ku4qo/MagicBox2.5/images/MagicBoxV2.5-PCBs_StackedFront-1024pix.jpg

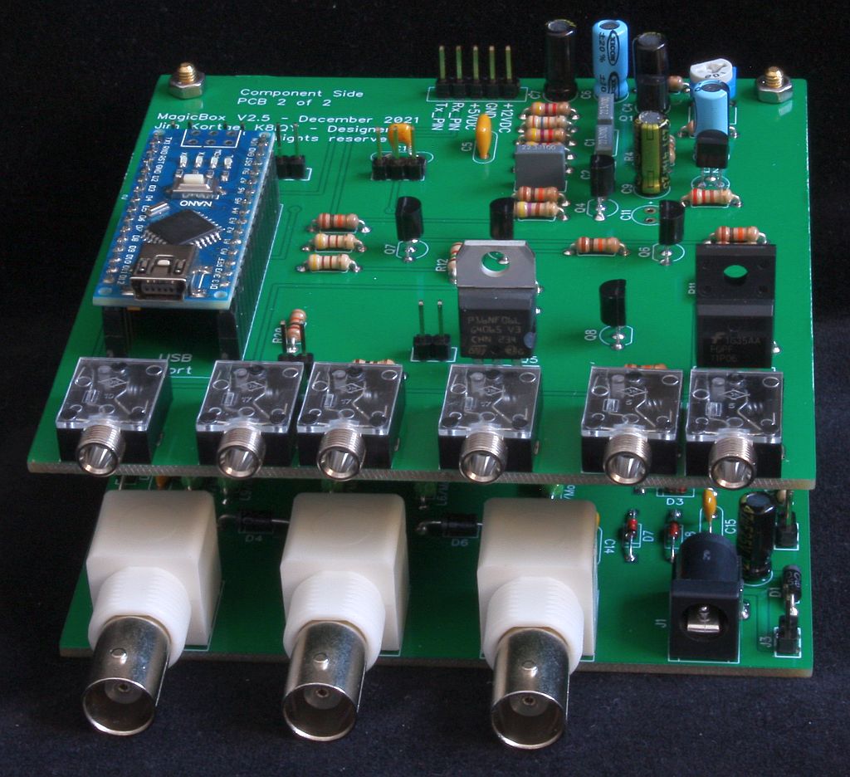
images/MagicBoxV2.5-PCBs_StackedFront-1024pix.jpg
