ku4qo/MagicBox2.5/images/MagicBoxV2.5A-PCB2_Stuffed-1024pix.jpg

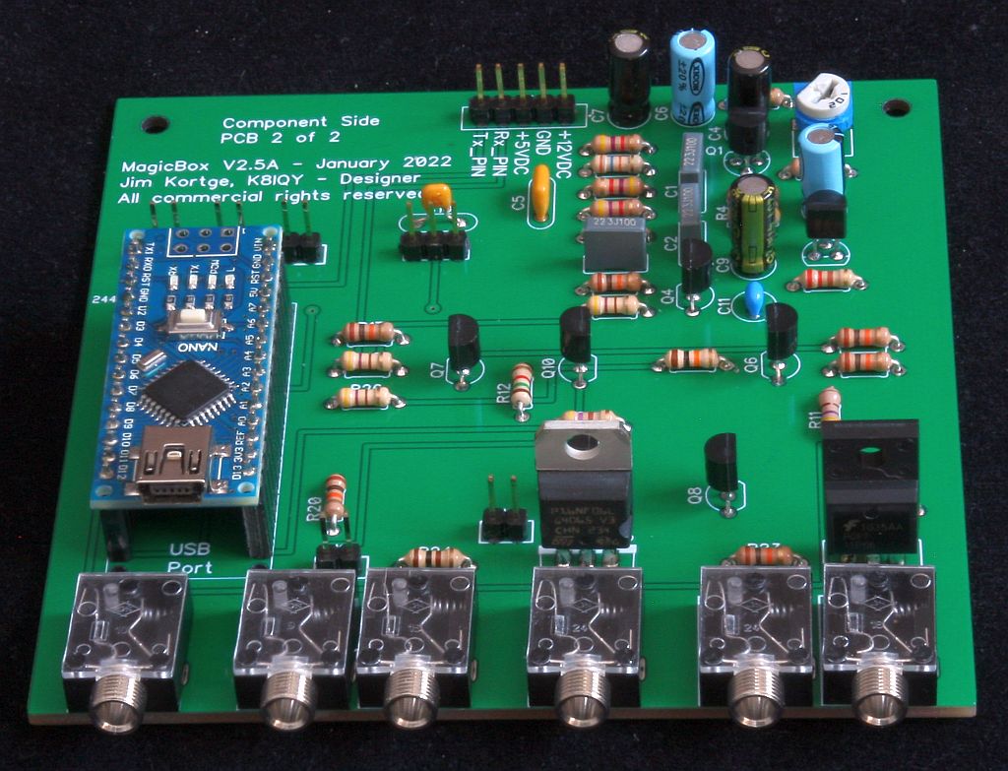
images/MagicBoxV2.5A-PCB2_Stuffed-1024pix.jpg
