ku4qo/MagicBox2.5/images/MagicBoxV2.X-BetaOS-LogicAnalyzer-30WPM_DIT.jpg

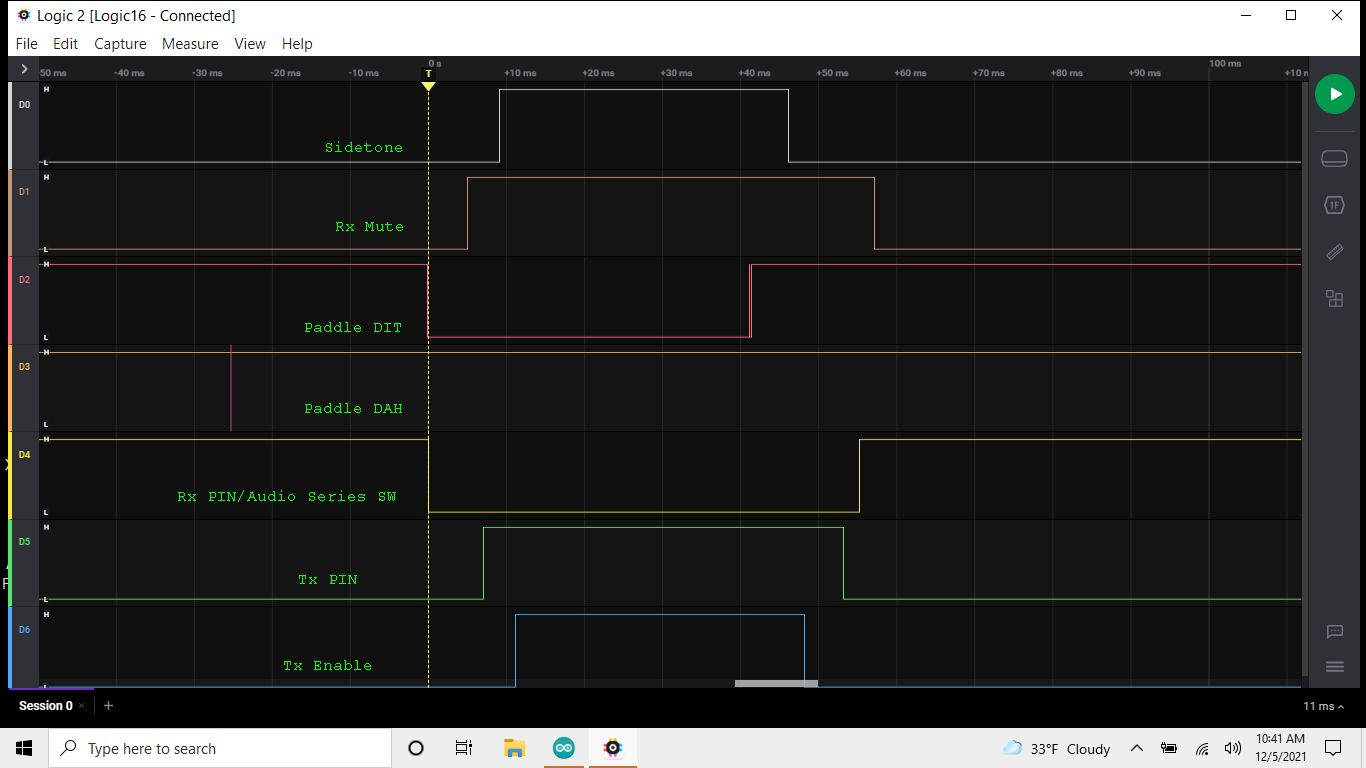
images/MagicBoxV2.X-BetaOS-LogicAnalyzer-30WPM_DIT.jpg
